mrWheel/softPowerLatch/assets/softPowerLatch_b.png

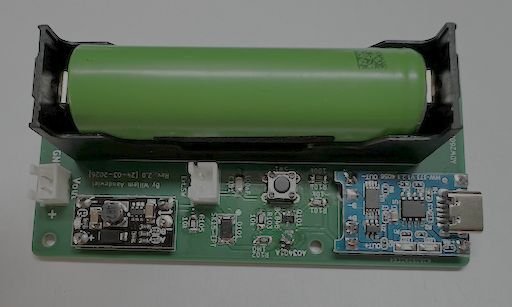
assets/softPowerLatch_b.png
