mrWheel/softPowerLatch/assets/softPowerLatch_Bottom.png

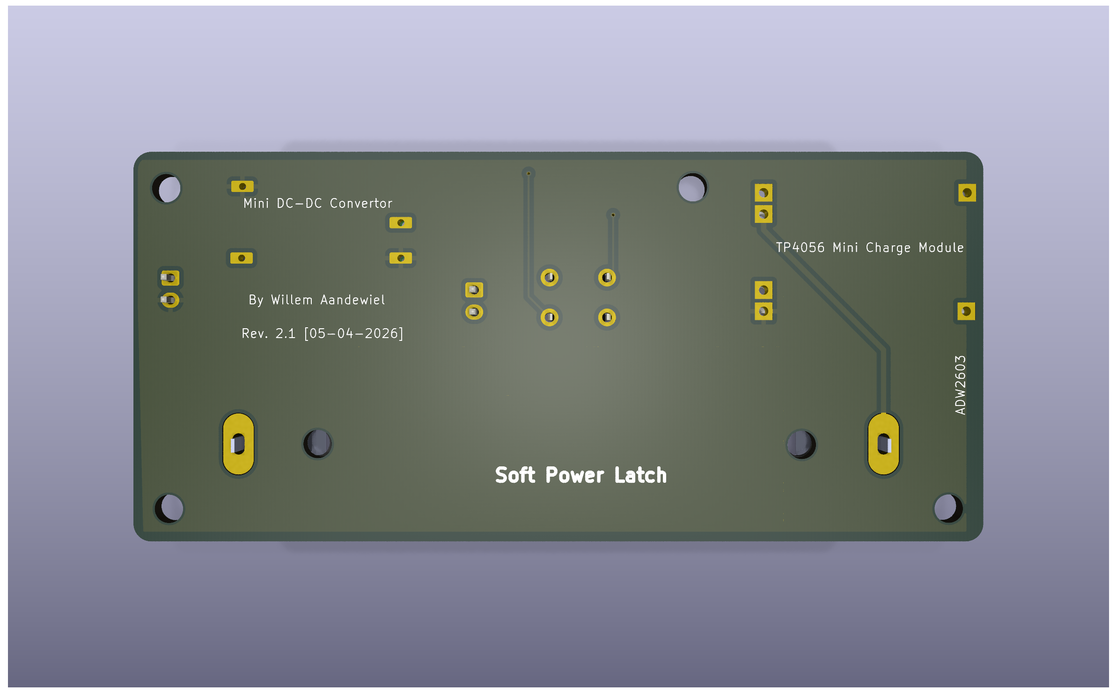
assets/softPowerLatch_Bottom.png
