mrWheel/softPowerLatch/assets/softPowerLatch_S1.png

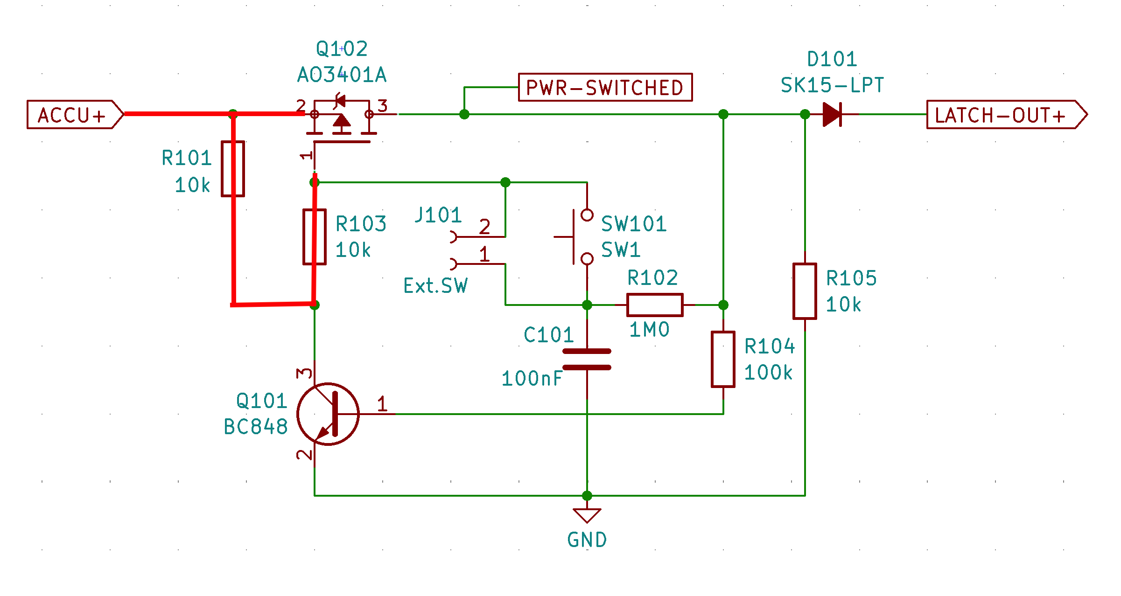
assets/softPowerLatch_S1.png
